calvin-mcd/travaulta/Images/DSCF4712.JPG

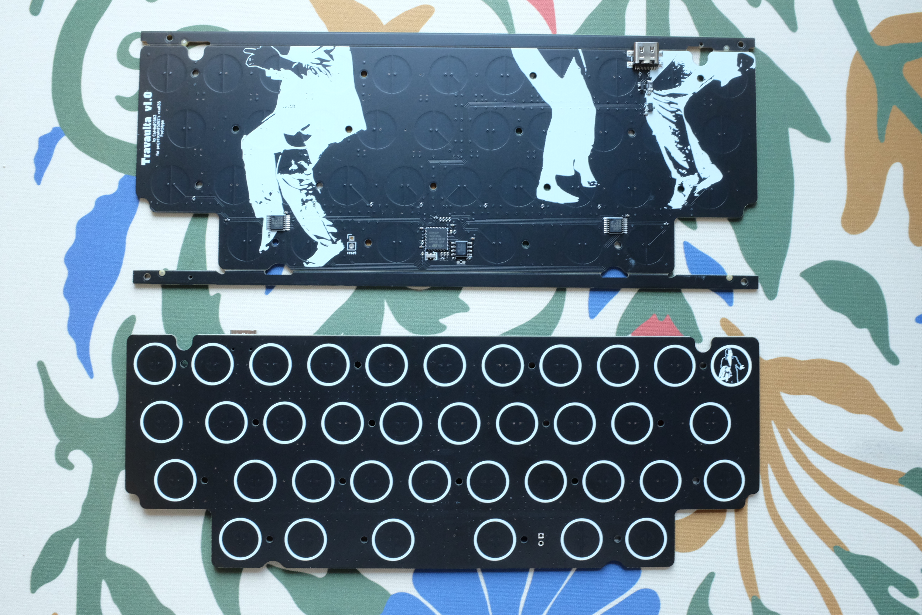
Images/DSCF4712.JPG
