calvin-mcd/travaulta/Project/travaulta HHKB/plates/production/plates/dxf/travaulta plate niz-B_Cu.dxf

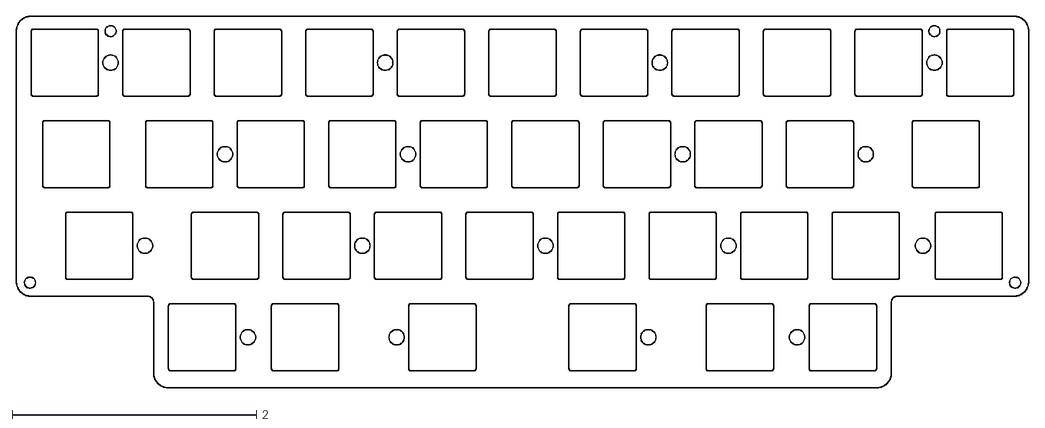
[picture p23: CAD file, 2023-08-20]
Project/travaulta HHKB/plates/production/plates/dxf/travaulta plate niz-B_Cu.dxf
8.30 x 3.05
