calvin-mcd/travaulta/Project/travaulta HHKB/plates/production/plates/dxf/travaulta plate niz-Edge_Cuts.dxf

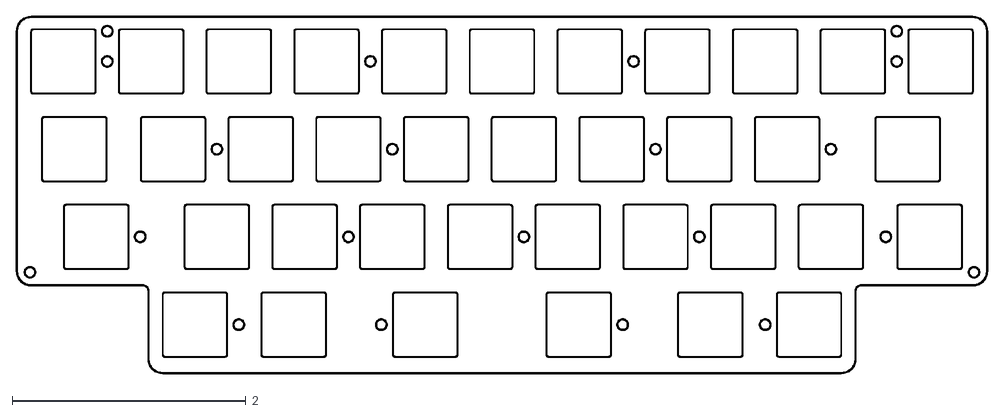
[picture p26: CAD file, 2023-08-20]
Project/travaulta HHKB/plates/production/plates/dxf/travaulta plate niz-Edge_Cuts.dxf
8.30 x 3.05
